Charading/Veil60/pcbs/Veil60.kicad_sch

## KiCad design pcbs/Veil60.kicad_sch (2025-10-09)

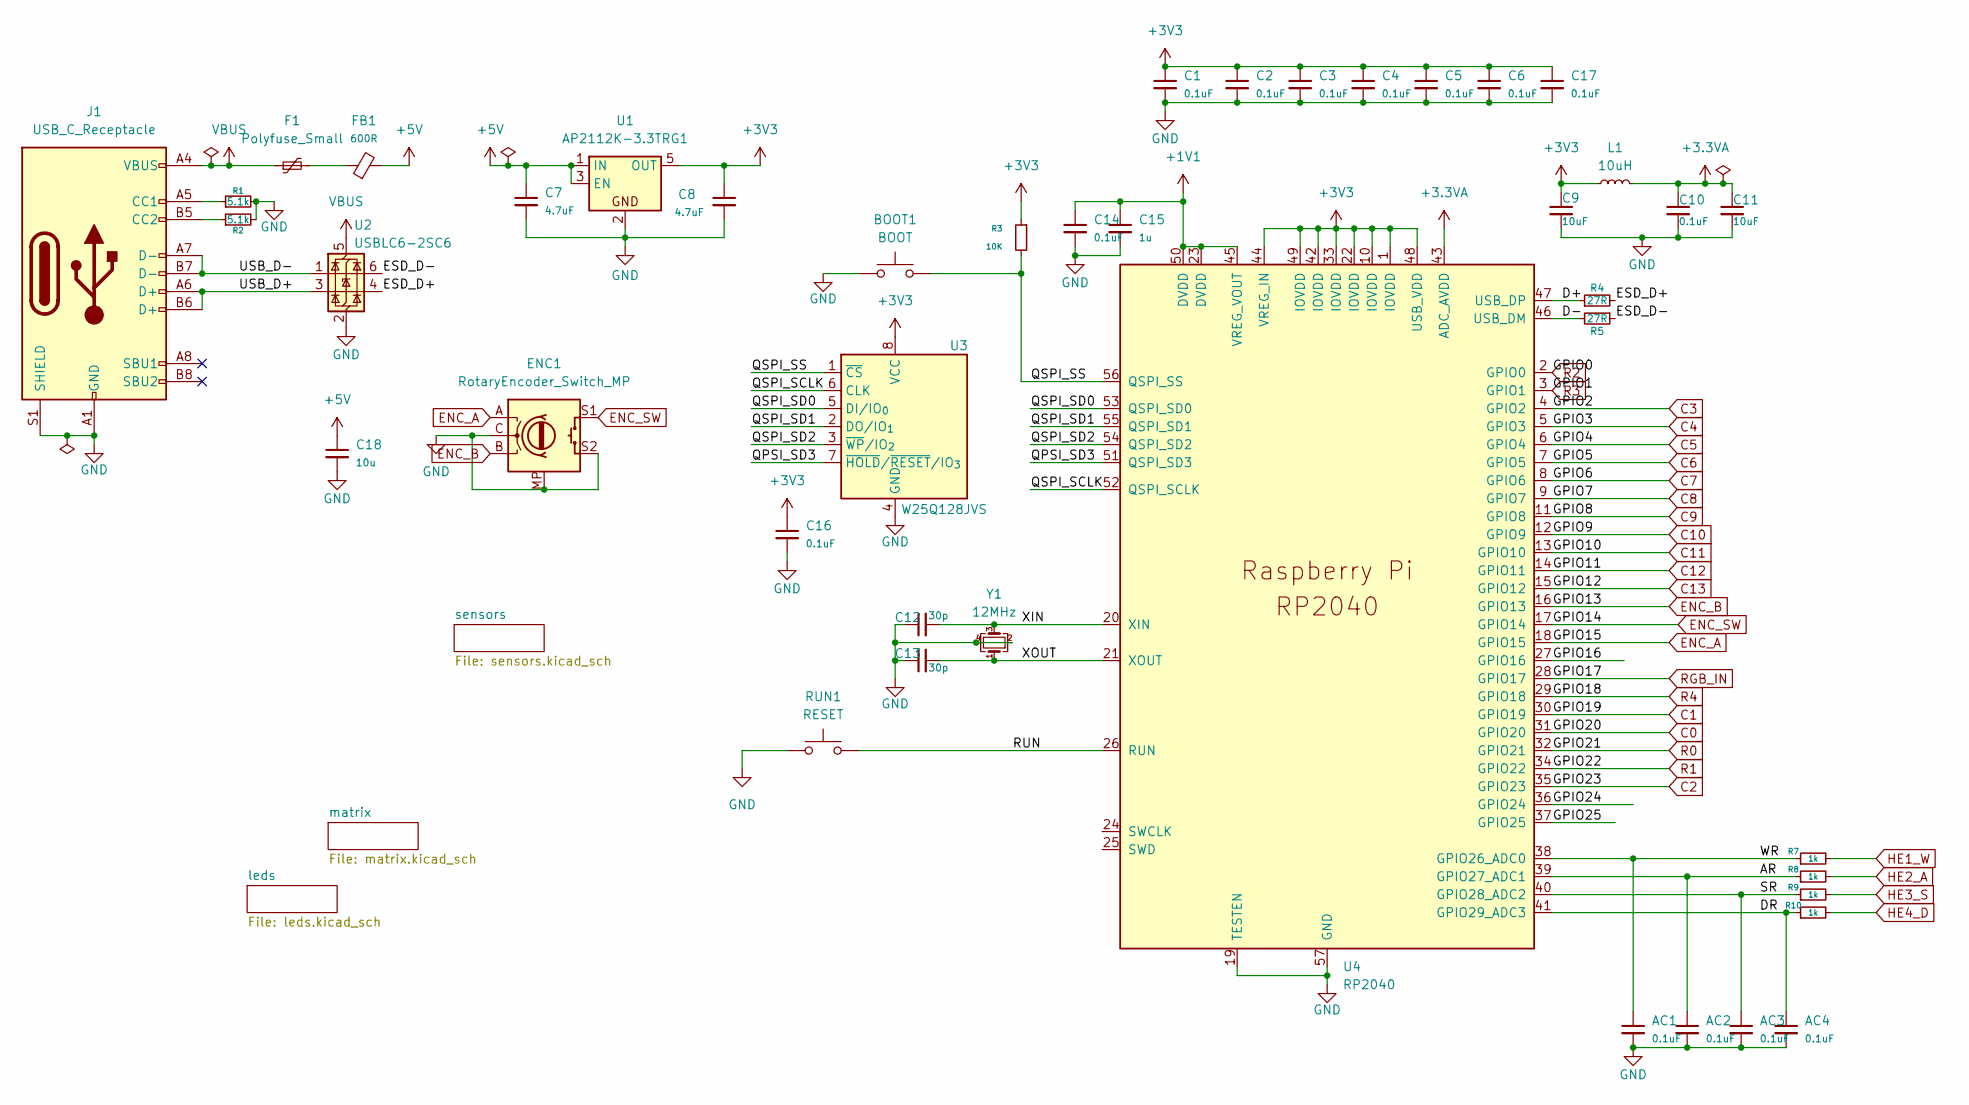
[picture p9: schematic Veil60.kicad_sch]

Parts:
AC1, AC2, AC3, AC4: 0.1uF; C_0402
BOOT1: BOOT; SW_SPST_EVQP2_MiddlePushTravel_H2.5mm
C1, C2, C3, C4, C5, C6, C14, C16, C17: 0.1uF; C_0402
C7, C8: 4.7uF; C_0805_2012Metric
C9, C11: 10uF; C_0603_1608Metric_Pad1.08x0.95mm_HandSolder
C10: 0.1uF; C_0603_1608Metric_Pad1.08x0.95mm_HandSolder
C12, C13: 30p; C_0603_1608Metric_Pad1.08x0.95mm_HandSolder
C15: 1u; C_0402
C18: 10u; C_0805_2012Metric
ENC1: RotaryEncoder_Switch_MP; RotaryEncoder_MX_EC11_CircularMountingHoles
F1: Polyfuse_Small; Fuse_0805_2012Metric
FB1: 600R; Ferrite_0805
J1: USB_C_Receptacle; USB_C_Receptacle_HRO_TYPE-C-31-M-12 (16P)
L1: 10uH; L_0805_2012Metric
R1, R2: 5.1k; R_0603
R3: 10K; R_0603
R4, R5: 27R; R_0603
R7, R8, R9, R10: 1k; R_0402
RUN1: RESET; SW_SPST_EVQP2_MiddlePushTravel_H2.5mm
U1: AP2112K-3.3TRG1; SOT-23-5
U2: USBLC6-2SC6; SOT-23-6
U3: W25Q128JVS; SOIC-8_5.3x5.3mm_P1.27mm
U4: RP2040; QFN-56-1EP_7x7mm_P0.4mm_EP3.2x3.2mm
Y1: 12MHz; Crystal_SMD_3225-4Pin_3.2x2.5mm

Connections:
+1V1: C14.1, C15.1, U4.23 (DVDD), U4.45 (VREG_VOUT), U4.50 (DVDD)
+3.3VA: C10.1, C11.1, L1.2, U4.43 (ADC_AVDD)
+3V3: C1.1, C2.1, C3.1, C4.1, C5.1, C6.1, C8.1, C9.1, C16.1, C17.1, L1.1, R3.1, U1.5 (OUT), U3.8 (VCC), U4.1 (IOVDD), U4.10 (IOVDD), U4.22 (IOVDD), U4.33 (IOVDD), U4.42 (IOVDD), U4.44 (VREG_IN), U4.48 (USB_VDD), U4.49 (IOVDD)
+5V: C7.1, C18.1, FB1.2, U1.1 (IN), U1.3 (EN)
AR: AC2.1, R8.1, U4.39 (GPIO27_ADC1)
C0: U4.31 (GPIO20)
C1: U4.30 (GPIO19)
C2: U4.35 (GPIO23)
C3: U4.4 (GPIO2)
C4: U4.5 (GPIO3)
C5: U4.6 (GPIO4)
C6: U4.7 (GPIO5)
C7: U4.8 (GPIO6)
C8: U4.9 (GPIO7)
C9: U4.11 (GPIO8)
C10: U4.12 (GPIO9)
C11: U4.13 (GPIO10)
C12: U4.14 (GPIO11)
C13: U4.15 (GPIO12)
D+: R4.1, U4.47 (USB_DP)
D-: R5.2, U4.46 (USB_DM)
DR: AC4.1, R10.1, U4.41 (GPIO29_ADC3)
ENC_A: ENC1.A, U4.18 (GPIO15)
ENC_B: ENC1.B, U4.16 (GPIO13)
ENC_SW: ENC1.S1, U4.17 (GPIO14)
ESD_D+: R4.2, U2.4 (I/O2)
ESD_D-: R5.1, U2.6 (I/O1)
GND: AC1.2, AC2.2, AC3.2, AC4.2, BOOT1.1, C1.2, C2.2, C3.2, C4.2, C5.2, C6.2, C7.2, C8.2, C9.2, C10.2, C11.2, C12.1, C13.1, C14.2, C15.2, C16.2, C17.2, C18.2, ENC1.C, ENC1.MP, ENC1.S2, J1.A1 (GND), J1.A12 (GND), J1.B1 (GND), J1.B12 (GND), J1.S1 (SHIELD), R1.2, R2.2, RUN1.1, U1.2, U2.2 (GND), U3.4 (GND), U4.19 (TESTEN), U4.57 (GND), Y1.2, Y1.4
GPIO16: U4.27 (GPIO16)
GPIO24: U4.36 (GPIO24)
GPIO25: U4.37 (GPIO25)
HE1_W: R7.2
HE2_A: R8.2
HE3_S: R9.2
HE4_D: R10.2
unnamed: F1.2, FB1.1
unnamed: J1.A5 (CC1), R1.1
unnamed: J1.B5 (CC2), R2.1
QPSI_SD3: U3.7 (~HOLD/~RESET/IO_{3}), U4.51 (QSPI_SD3)
QSPI_SCLK: U3.6 (CLK), U4.52 (QSPI_SCLK)
QSPI_SD0: U3.5 (DI/IO_{0}), U4.53 (QSPI_SD0)
QSPI_SD1: U3.2 (DO/IO_{1}), U4.55 (QSPI_SD1)
QSPI_SD2: U3.3 (~WP/IO_{2}), U4.54 (QSPI_SD2)
QSPI_SS: BOOT1.2, R3.2, U3.1 (~CS), U4.56 (QSPI_SS)
R0: U4.32 (GPIO21)
R1: U4.34 (GPIO22)
R2: U4.2 (GPIO0)
R3: U4.3 (GPIO1)
R4: U4.29 (GPIO18)
RGB_IN: U4.28 (GPIO17)
RUN: RUN1.2, U4.26 (RUN)
SR: AC3.1, R9.1, U4.40 (GPIO28_ADC2)
USB_D+: J1.A6 (D+), J1.B6 (D+), U2.3 (I/O2)
USB_D-: J1.A7 (D-), J1.B7 (D-), U2.1 (I/O1)
VBUS: F1.1, J1.A4 (VBUS), J1.A9 (VBUS), J1.B4 (VBUS), J1.B9 (VBUS), U2.5 (VBUS)
WR: AC1.1, R7.1, U4.38 (GPIO26_ADC0)
XIN: C12.2, U4.20 (XIN), Y1.3
XOUT: C13.2, U4.21 (XOUT), Y1.1
