Charading/Veil60/pcbs/leds.kicad_sch

## KiCad design pcbs/leds.kicad_sch (2025-10-09)

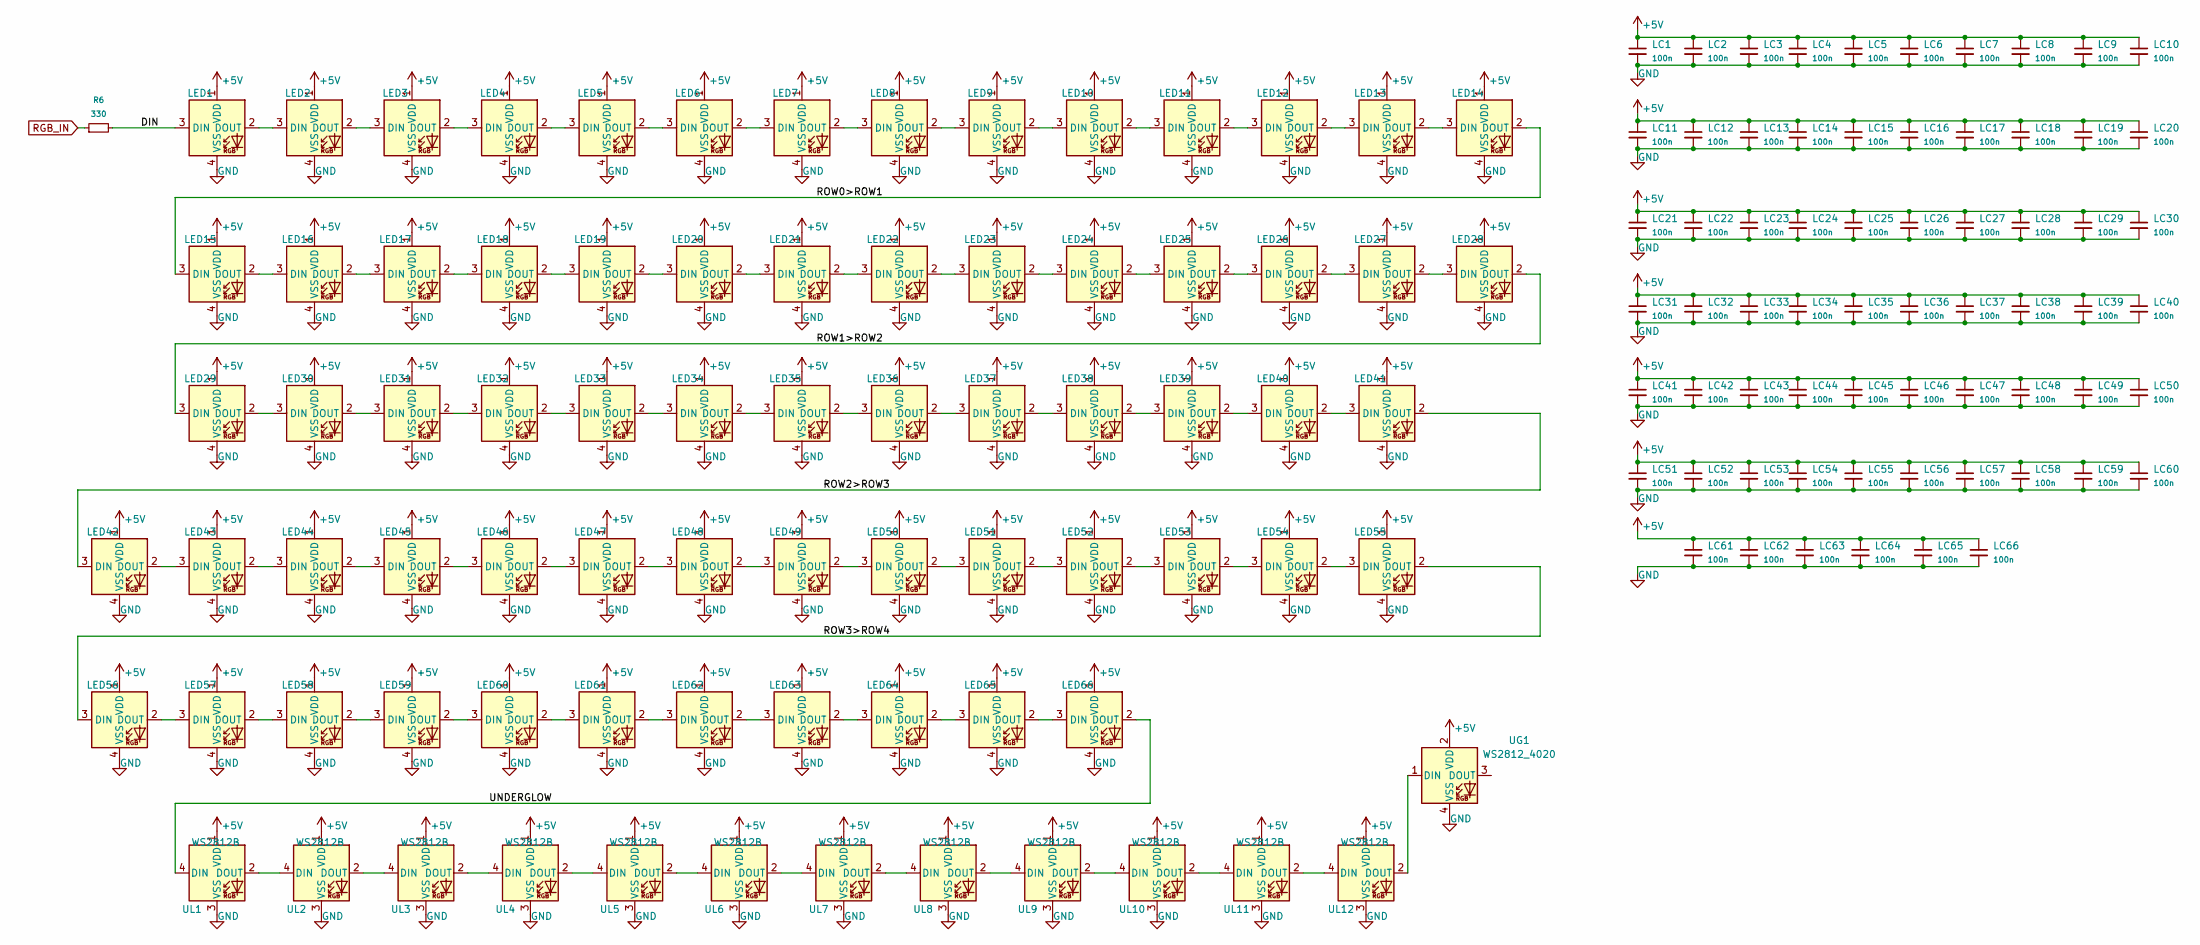
[picture p10: schematic leds.kicad_sch]

Parts:
LC1, LC2, LC3, LC4, LC5, LC6, LC7, LC8, LC9, LC10, LC11, LC12, LC13, LC14, LC15, LC16, LC17, LC18, LC19, LC20, LC21, LC22, LC23, LC24, LC25, LC26, LC27, LC28, LC29, LC30, LC31, LC32, LC33, LC34, LC35, LC36, LC37, LC38, LC39, LC40, LC41, LC42, LC43, LC44, LC45, LC46, LC47, LC48, LC49, LC50, LC51, LC52, LC53, LC54, LC55, LC56, LC57, LC58, LC59, LC60, LC61, LC62, LC63, LC64, LC65, LC66: 100n; C_0402_1005Metric_Pad0.74x0.62mm_HandSolder
LED1, LED2, LED3, LED4, LED5, LED6, LED7, LED8, LED9, LED10, LED11, LED12, LED13, LED14, LED15, LED16, LED17, LED18, LED19, LED20, LED21, LED22, LED23, LED24, LED25, LED26, LED27, LED28, LED29, LED30, LED31, LED32, LED33, LED34, LED35, LED36, LED37, LED38, LED39, LED40, LED41, LED42, LED43, LED44, LED45, LED46, LED47, LED48, LED49, LED50, LED51, LED52, LED53, LED54, LED55, LED56, LED57, LED58, LED59, LED60, LED61, LED62, LED63, LED64, LED65, LED66: SK6812MINI-E; LED_6028R
R6: 330; R_0603
UG1: WS2812_4020; LED_WS2812_4020
UL1, UL2, UL3, UL4, UL5, UL6, UL7, UL8, UL9, UL10, UL11, UL12: WS2812B; LED_WS2812B_PLCC4_5.0x5.0mm_P3.2mm

Connections:
+5V: LC1.1, LC2.1, LC3.1, LC4.1, LC5.1, LC6.1, LC7.1, LC8.1, LC9.1, LC10.1, LC11.1, LC12.1, LC13.1, LC14.1, LC15.1, LC16.1, LC17.1, LC18.1, LC19.1, LC20.1, LC21.1, LC22.1, LC23.1, LC24.1, LC25.1, LC26.1, LC27.1, LC28.1, LC29.1, LC30.1, LC31.1, LC32.1, LC33.1, LC34.1, LC35.1, LC36.1, LC37.1, LC38.1, LC39.1, LC40.1, LC41.1, LC42.1, LC43.1, LC44.1, LC45.1, LC46.1, LC47.1, LC48.1, LC49.1, LC50.1, LC51.1, LC52.1, LC53.1, LC54.1, LC55.1, LC56.1, LC57.1, LC58.1, LC59.1, LC60.1, LC61.1, LC62.1, LC63.1, LC64.1, LC65.1, LC66.1, LED1.1 (VDD), LED2.1 (VDD), LED3.1 (VDD), LED4.1 (VDD), LED5.1 (VDD), LED6.1 (VDD), LED7.1 (VDD), LED8.1 (VDD), LED9.1 (VDD), LED10.1 (VDD), LED11.1 (VDD), LED12.1 (VDD), LED13.1 (VDD), LED14.1 (VDD), LED15.1 (VDD), LED16.1 (VDD), LED17.1 (VDD), LED18.1 (VDD), LED19.1 (VDD), LED20.1 (VDD), LED21.1 (VDD), LED22.1 (VDD), LED23.1 (VDD), LED24.1 (VDD), LED25.1 (VDD), LED26.1 (VDD), LED27.1 (VDD), LED28.1 (VDD), LED29.1 (VDD), LED30.1 (VDD), LED31.1 (VDD), LED32.1 (VDD), LED33.1 (VDD), LED34.1 (VDD), LED35.1 (VDD), LED36.1 (VDD), LED37.1 (VDD), LED38.1 (VDD), LED39.1 (VDD), LED40.1 (VDD), LED41.1 (VDD), LED42.1 (VDD), LED43.1 (VDD), LED44.1 (VDD), LED45.1 (VDD), LED46.1 (VDD), LED47.1 (VDD), LED48.1 (VDD), LED49.1 (VDD), LED50.1 (VDD), LED51.1 (VDD), LED52.1 (VDD), LED53.1 (VDD), LED54.1 (VDD), LED55.1 (VDD), LED56.1 (VDD), LED57.1 (VDD), LED58.1 (VDD), LED59.1 (VDD), LED60.1 (VDD), LED61.1 (VDD), LED62.1 (VDD), LED63.1 (VDD), LED64.1 (VDD), LED65.1 (VDD), LED66.1 (VDD), UG1.2 (VDD), UL1.1 (VDD), UL2.1 (VDD), UL3.1 (VDD), UL4.1 (VDD), UL5.1 (VDD), UL6.1 (VDD), UL7.1 (VDD), UL8.1 (VDD), UL9.1 (VDD), UL10.1 (VDD), UL11.1 (VDD), UL12.1 (VDD)
DIN: LED1.3 (DIN), R6.2
GND: LC1.2, LC2.2, LC3.2, LC4.2, LC5.2, LC6.2, LC7.2, LC8.2, LC9.2, LC10.2, LC11.2, LC12.2, LC13.2, LC14.2, LC15.2, LC16.2, LC17.2, LC18.2, LC19.2, LC20.2, LC21.2, LC22.2, LC23.2, LC24.2, LC25.2, LC26.2, LC27.2, LC28.2, LC29.2, LC30.2, LC31.2, LC32.2, LC33.2, LC34.2, LC35.2, LC36.2, LC37.2, LC38.2, LC39.2, LC40.2, LC41.2, LC42.2, LC43.2, LC44.2, LC45.2, LC46.2, LC47.2, LC48.2, LC49.2, LC50.2, LC51.2, LC52.2, LC53.2, LC54.2, LC55.2, LC56.2, LC57.2, LC58.2, LC59.2, LC60.2, LC61.2, LC62.2, LC63.2, LC64.2, LC65.2, LC66.2, LED1.4 (VSS), LED2.4 (VSS), LED3.4 (VSS), LED4.4 (VSS), LED5.4 (VSS), LED6.4 (VSS), LED7.4 (VSS), LED8.4 (VSS), LED9.4 (VSS), LED10.4 (VSS), LED11.4 (VSS), LED12.4 (VSS), LED13.4 (VSS), LED14.4 (VSS), LED15.4 (VSS), LED16.4 (VSS), LED17.4 (VSS), LED18.4 (VSS), LED19.4 (VSS), LED20.4 (VSS), LED21.4 (VSS), LED22.4 (VSS), LED23.4 (VSS), LED24.4 (VSS), LED25.4 (VSS), LED26.4 (VSS), LED27.4 (VSS), LED28.4 (VSS), LED29.4 (VSS), LED30.4 (VSS), LED31.4 (VSS), LED32.4 (VSS), LED33.4 (VSS), LED34.4 (VSS), LED35.4 (VSS), LED36.4 (VSS), LED37.4 (VSS), LED38.4 (VSS), LED39.4 (VSS), LED40.4 (VSS), LED41.4 (VSS), LED42.4 (VSS), LED43.4 (VSS), LED44.4 (VSS), LED45.4 (VSS), LED46.4 (VSS), LED47.4 (VSS), LED48.4 (VSS), LED49.4 (VSS), LED50.4 (VSS), LED51.4 (VSS), LED52.4 (VSS), LED53.4 (VSS), LED54.4 (VSS), LED55.4 (VSS), LED56.4 (VSS), LED57.4 (VSS), LED58.4 (VSS), LED59.4 (VSS), LED60.4 (VSS), LED61.4 (VSS), LED62.4 (VSS), LED63.4 (VSS), LED64.4 (VSS), LED65.4 (VSS), LED66.4 (VSS), UG1.4 (VSS), UL1.3 (VSS), UL2.3 (VSS), UL3.3 (VSS), UL4.3 (VSS), UL5.3 (VSS), UL6.3 (VSS), UL7.3 (VSS), UL8.3 (VSS), UL9.3 (VSS), UL10.3 (VSS), UL11.3 (VSS), UL12.3 (VSS)
unnamed: LED1.2 (DOUT), LED2.3 (DIN)
unnamed: LED2.2 (DOUT), LED3.3 (DIN)
unnamed: LED3.2 (DOUT), LED4.3 (DIN)
unnamed: LED4.2 (DOUT), LED5.3 (DIN)
unnamed: LED5.2 (DOUT), LED6.3 (DIN)
unnamed: LED6.2 (DOUT), LED7.3 (DIN)
unnamed: LED7.2 (DOUT), LED8.3 (DIN)
unnamed: LED8.2 (DOUT), LED9.3 (DIN)
unnamed: LED10.2 (DOUT), LED11.3 (DIN)
unnamed: LED9.2 (DOUT), LED10.3 (DIN)
unnamed: LED11.2 (DOUT), LED12.3 (DIN)
unnamed: LED12.2 (DOUT), LED13.3 (DIN)
unnamed: LED13.2 (DOUT), LED14.3 (DIN)
unnamed: LED15.2 (DOUT), LED16.3 (DIN)
unnamed: LED16.2 (DOUT), LED17.3 (DIN)
unnamed: LED17.2 (DOUT), LED18.3 (DIN)
unnamed: LED18.2 (DOUT), LED19.3 (DIN)
unnamed: LED19.2 (DOUT), LED20.3 (DIN)
unnamed: LED20.2 (DOUT), LED21.3 (DIN)
unnamed: LED21.2 (DOUT), LED22.3 (DIN)
unnamed: LED22.2 (DOUT), LED23.3 (DIN)
unnamed: LED23.2 (DOUT), LED24.3 (DIN)
unnamed: LED24.2 (DOUT), LED25.3 (DIN)
unnamed: LED25.2 (DOUT), LED26.3 (DIN)
unnamed: LED26.2 (DOUT), LED27.3 (DIN)
unnamed: LED27.2 (DOUT), LED28.3 (DIN)
unnamed: LED29.2 (DOUT), LED30.3 (DIN)
unnamed: LED30.2 (DOUT), LED31.3 (DIN)
unnamed: LED31.2 (DOUT), LED32.3 (DIN)
unnamed: LED32.2 (DOUT), LED33.3 (DIN)
unnamed: LED33.2 (DOUT), LED34.3 (DIN)
unnamed: LED34.2 (DOUT), LED35.3 (DIN)
unnamed: LED35.2 (DOUT), LED36.3 (DIN)
unnamed: LED36.2 (DOUT), LED37.3 (DIN)
unnamed: LED37.2 (DOUT), LED38.3 (DIN)
unnamed: LED38.2 (DOUT), LED39.3 (DIN)
unnamed: LED39.2 (DOUT), LED40.3 (DIN)
unnamed: LED40.2 (DOUT), LED41.3 (DIN)
unnamed: LED42.2 (DOUT), LED43.3 (DIN)
unnamed: LED43.2 (DOUT), LED44.3 (DIN)
unnamed: LED44.2 (DOUT), LED45.3 (DIN)
unnamed: LED45.2 (DOUT), LED46.3 (DIN)
unnamed: LED46.2 (DOUT), LED47.3 (DIN)
unnamed: LED47.2 (DOUT), LED48.3 (DIN)
unnamed: LED48.2 (DOUT), LED49.3 (DIN)
unnamed: LED49.2 (DOUT), LED50.3 (DIN)
unnamed: LED50.2 (DOUT), LED51.3 (DIN)
unnamed: LED51.2 (DOUT), LED52.3 (DIN)
unnamed: LED52.2 (DOUT), LED53.3 (DIN)
unnamed: LED53.2 (DOUT), LED54.3 (DIN)
unnamed: LED54.2 (DOUT), LED55.3 (DIN)
unnamed: LED56.2 (DOUT), LED57.3 (DIN)
unnamed: LED57.2 (DOUT), LED58.3 (DIN)
unnamed: LED58.2 (DOUT), LED59.3 (DIN)
unnamed: LED59.2 (DOUT), LED60.3 (DIN)
unnamed: LED60.2 (DOUT), LED61.3 (DIN)
unnamed: LED61.2 (DOUT), LED62.3 (DIN)
unnamed: LED62.2 (DOUT), LED63.3 (DIN)
unnamed: LED63.2 (DOUT), LED64.3 (DIN)
unnamed: LED64.2 (DOUT), LED65.3 (DIN)
unnamed: LED65.2 (DOUT), LED66.3 (DIN)
unnamed: UG1.1 (DIN), UL12.2 (DOUT)
unnamed: UL1.2 (DOUT), UL2.4 (DIN)
unnamed: UL2.2 (DOUT), UL3.4 (DIN)
unnamed: UL3.2 (DOUT), UL4.4 (DIN)
unnamed: UL4.2 (DOUT), UL5.4 (DIN)
unnamed: UL5.2 (DOUT), UL6.4 (DIN)
unnamed: UL6.2 (DOUT), UL7.4 (DIN)
unnamed: UL7.2 (DOUT), UL8.4 (DIN)
unnamed: UL8.2 (DOUT), UL9.4 (DIN)
unnamed: UL10.2 (DOUT), UL11.4 (DIN)
unnamed: UL9.2 (DOUT), UL10.4 (DIN)
unnamed: UL11.2 (DOUT), UL12.4 (DIN)
RGB_IN: R6.1
ROW0>ROW1: LED14.2 (DOUT), LED15.3 (DIN)
ROW1>ROW2: LED28.2 (DOUT), LED29.3 (DIN)
ROW2>ROW3: LED41.2 (DOUT), LED42.3 (DIN)
ROW3>ROW4: LED55.2 (DOUT), LED56.3 (DIN)
UNDERGLOW: LED66.2 (DOUT), UL1.4 (DIN)
