Charading/Veil60/pcbs/sensors.kicad_sch

## KiCad design pcbs/sensors.kicad_sch (2025-10-09)

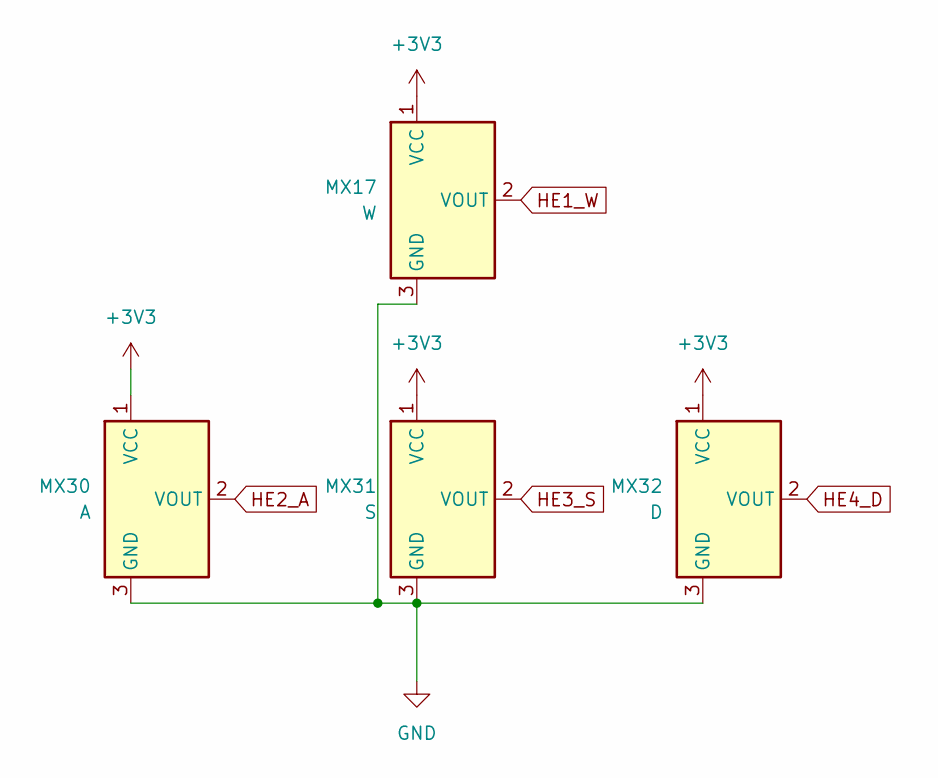
[picture p12: schematic sensors.kicad_sch]

Parts:
MX17: W; SW_MX_HE_90deg_1u
MX30: A; SW_MX_HE_90deg_1u
MX31: S; SW_MX_HE_90deg_1u
MX32: D; SW_MX_HE_90deg_1u

Connections:
+3V3: MX17.1 (VCC), MX30.1 (VCC), MX31.1 (VCC), MX32.1 (VCC)
GND: MX17.3 (GND), MX30.3 (GND), MX31.3 (GND), MX32.3 (GND)
HE1_W: MX17.2 (VOUT)
HE2_A: MX30.2 (VOUT)
HE3_S: MX31.2 (VOUT)
HE4_D: MX32.2 (VOUT)
